AmirHassenBenHassine/orion-energy-meter/test/test_embedded/test_ota/test_ota.cpp

#include <Arduino.h>
#include <ArduinoJson.h>
#include <HTTPClient.h>
#include <Update.h>
#include <WiFi.h>
#include <WiFiClientSecure.h>
#include <esp_ota_ops.h>
#include <esp_partition.h>
#include <unity.h>

// #define TEST_WIFI_SSID "TUNISIETELECOM-2.4G-nG46_Plus"
// #define TEST_WIFI_PASS "KF39UwaM"

#define TEST_WIFI_SSID "Amir"
#define TEST_WIFI_PASS "beethoveen"

// Your GitHub repo details
#define GITHUB_USER "AmirHassenBenHassine"
#define GITHUB_REPO "OTA_Github"
#define GITHUB_BRANCH "main"
#define FIRMWARE_BIN_NAME "finalOrion_transmiter.ino1.bin"
#define VERSION_JSON_NAME "version.json"

#define CURRENT_VERSION "1.0.0"  // Change this to test updates

bool isMeasuring = false;  // Add to global scope

// URLs
String FIRMWARE_URL = "https://raw.githubusercontent.com/" + String(GITHUB_USER) + "/" + 
                      String(GITHUB_REPO) + "/" + String(GITHUB_BRANCH) + "/" + FIRMWARE_BIN_NAME;

String VERSION_JSON_URL = "https://raw.githubusercontent.com/" + String(GITHUB_USER) + "/" + 
                          String(GITHUB_REPO) + "/" + String(GITHUB_BRANCH) + "/" + VERSION_JSON_NAME;

static const char GITHUB_ROOT_CA[] PROGMEM = R"EOF(
-----BEGIN CERTIFICATE-----
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
MrY=
-----END CERTIFICATE-----
)EOF";

// Let's Encrypt CA (for your VPS MQTT broker)
static const char LETSENCRYPT_CA_CERT[] PROGMEM = R"EOF(
-----BEGIN CERTIFICATE-----
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
-----END CERTIFICATE-----
)EOF";

WiFiClientSecure secureClient;

void connectWiFi() {
  if (WiFi.status() == WL_CONNECTED)
    return;
  WiFi.mode(WIFI_STA);
  WiFi.begin(TEST_WIFI_SSID, TEST_WIFI_PASS);

  unsigned long start = millis();
  while (WiFi.status() != WL_CONNECTED && (millis() - start) < 30000) {
    delay(500);
    Serial.print(".");
  }
  Serial.printf("\nWiFi connected. IP: %s\n",
                WiFi.localIP().toString().c_str());
}

void syncTime() {
  Serial.print("Syncing time...");
  configTime(0, 0, "pool.ntp.org", "time.nist.gov");

  time_t now = time(nullptr);
  int attempts = 0;
  while (now < 1700000000 && attempts < 30) {
    delay(500);
    Serial.print(".");
    now = time(nullptr);
    attempts++;
  }

  if (now > 1700000000) {
    Serial.printf(" Done! Time: %s", ctime(&now));
  } else {
    Serial.println(" FAILED!");
  }
}

bool isTimeSynced() {
  time_t now = time(nullptr);
  return now > 1700000000;
}

void setUp(void) {}
void tearDown(void) {}

// =============================================================================
// VERSION COMPARISON TESTS (No network needed)
// =============================================================================

int compareVersions(const String &v1, const String &v2) {
  int major1 = 0, minor1 = 0, patch1 = 0;
  int major2 = 0, minor2 = 0, patch2 = 0;

  sscanf(v1.c_str(), "%d.%d.%d", &major1, &minor1, &patch1);
  sscanf(v2.c_str(), "%d.%d.%d", &major2, &minor2, &patch2);

  if (major1 != major2)
    return major1 - major2;
  if (minor1 != minor2)
    return minor1 - minor2;
  return patch1 - patch2;
}

void test_version_compare_equal(void) {
  TEST_ASSERT_EQUAL(0, compareVersions("1.0.0", "1.0.0"));
}

void test_version_compare_major_greater(void) {
  TEST_ASSERT_GREATER_THAN(0, compareVersions("2.0.0", "1.0.0"));
}

void test_version_compare_major_less(void) {
  TEST_ASSERT_LESS_THAN(0, compareVersions("1.0.0", "2.0.0"));
}

void test_version_compare_minor_greater(void) {
  TEST_ASSERT_GREATER_THAN(0, compareVersions("1.2.0", "1.1.0"));
}

void test_version_compare_minor_less(void) {
  TEST_ASSERT_LESS_THAN(0, compareVersions("1.1.0", "1.2.0"));
}

void test_version_compare_patch_greater(void) {
  TEST_ASSERT_GREATER_THAN(0, compareVersions("1.0.2", "1.0.1"));
}

void test_version_compare_patch_less(void) {
  TEST_ASSERT_LESS_THAN(0, compareVersions("1.0.1", "1.0.2"));
}

void test_version_compare_complex(void) {
  TEST_ASSERT_GREATER_THAN(0, compareVersions("2.1.0", "1.9.9"));
  TEST_ASSERT_LESS_THAN(0, compareVersions("1.9.9", "2.0.0"));
  TEST_ASSERT_EQUAL(0, compareVersions("10.20.30", "10.20.30"));
}

// =============================================================================
// UPDATE SYSTEM TESTS (No network needed)
// =============================================================================

void test_update_partition_exists(void) {
  const esp_partition_t *partition = esp_ota_get_next_update_partition(NULL);
  TEST_ASSERT_NOT_NULL_MESSAGE(partition, "No OTA partition found");

  Serial.printf("OTA partition: %s, size: %lu bytes\n", partition->label,
                (unsigned long)partition->size);
}

void test_update_has_enough_space(void) {
  const esp_partition_t *partition = esp_ota_get_next_update_partition(NULL);
  TEST_ASSERT_NOT_NULL(partition);

  // Should have at least 1MB for firmware
  TEST_ASSERT_GREATER_THAN(1000000, partition->size);
}

void test_update_begin_end(void) {
  size_t testSize = 1024;

  bool beginResult = Update.begin(testSize);
  TEST_ASSERT_TRUE_MESSAGE(beginResult, "Update.begin() failed");

  Update.abort();
}

void test_running_partition_valid(void) {
  const esp_partition_t *running = esp_ota_get_running_partition();
  TEST_ASSERT_NOT_NULL_MESSAGE(running, "Cannot get running partition");

  Serial.printf("Running from: %s\n", running->label);
}

// =============================================================================
// HTTPS CONNECTION TESTS (Verify GitHub will work)
// =============================================================================

void test_https_github_with_correct_ca(void) {
  secureClient.setCACert(GITHUB_ROOT_CA);

  bool connected = secureClient.connect("raw.githubusercontent.com", 443);

  TEST_ASSERT_TRUE_MESSAGE(connected, "GitHub HTTPS connection failed");

  Serial.println("GitHub with DigiCert G2 CA: OK");

  secureClient.stop();
}

void test_https_fetch_from_github(void) {
  Serial.println("\n--- Testing GitHub HTTPS Fetch ---");
  
  HTTPClient http;
  WiFiClientSecure client;
  
  // ✅ Skip certificate validation (simple and works)
  client.setInsecure();
  
  // Use a simple, reliable GitHub URL
  String url = "https://raw.githubusercontent.com/espressif/arduino-esp32/master/package.json";
  
  Serial.printf("Fetching: %s\n", url.c_str());
  
  http.begin(client, url);
  http.setTimeout(15000);  // 15 second timeout
  http.setFollowRedirects(HTTPC_STRICT_FOLLOW_REDIRECTS);
  
  Serial.println("Sending GET request...");
  int httpCode = http.GET();
  
  Serial.printf("HTTP Response: %d\n", httpCode);
  
  if (httpCode != 200) {
    Serial.printf("Error: %s\n", http.errorToString(httpCode).c_str());
  }
  
  TEST_ASSERT_EQUAL_MESSAGE(200, httpCode, "GitHub fetch failed");
  
  if (httpCode == 200) {
    String payload = http.getString();
    Serial.printf("✅ Downloaded %d bytes from GitHub\n", payload.length());
    Serial.println("First 100 chars:");
    Serial.println(payload.substring(0, 100));
  }
  
  http.end();
  Serial.println("GitHub HTTPS test: PASSED");
}

// void test_https_connection_with_ca(void) {
//   // Verify time is synced first
//   TEST_ASSERT_TRUE_MESSAGE(isTimeSynced(),
//                            "Time not synced - cert verification will fail");
//   secureClient.setCACert(ISRG_ROOT_X1);
//
//   bool connected = secureClient.connect("www.google.com", 443);
//
//   TEST_ASSERT_TRUE_MESSAGE(connected, "HTTPS connection failed");
//
//   secureClient.stop();
// }
//
// void test_https_github_connection(void) {
//   // Verify time is synced first
//   TEST_ASSERT_TRUE_MESSAGE(isTimeSynced(),
//                            "Time not synced - cert verification will fail");
//   secureClient.setCACert(ISRG_ROOT_X1);
//   bool connected = secureClient.connect("raw.githubusercontent.com", 443);
//
//   TEST_ASSERT_TRUE_MESSAGE(connected, "GitHub HTTPS connection failed");
//
//   if (connected) {
//     Serial.println("GitHub connection: OK (Let's Encrypt CA works!)");
//   }
//
//   secureClient.stop();
// }
//
// void test_https_fetch_small_file(void) {
//   HTTPClient http;
//   TEST_ASSERT_TRUE_MESSAGE(isTimeSynced(),
//                            "Time not synced - cert verification will fail");
//   secureClient.setCACert(ISRG_ROOT_X1);
//
//   http.begin(secureClient, "https://raw.githubusercontent.com/espressif/"
//                            "arduino-esp32/master/package.json");
//
//   int httpCode = http.GET();
//
//   TEST_ASSERT_EQUAL_MESSAGE(200, httpCode, "Failed to fetch file from
//   GitHub");
//
//   if (httpCode == 200) {
//     String payload = http.getString();
//     TEST_ASSERT_GREATER_THAN(0, payload.length());
//     Serial.printf("Fetched %d bytes from GitHub\n", payload.length());
//   }
//
//   http.end();
// }
//
// =============================================================================
// JSON PARSING TESTS (Simulates version.json parsing)
// =============================================================================

void test_github_reachable(void) {
  WiFiClientSecure client;
  client.setInsecure();  // Skip cert validation for simplicity
  
  bool connected = client.connect("raw.githubusercontent.com", 443);
  TEST_ASSERT_TRUE_MESSAGE(connected, "Cannot reach GitHub");
  
  client.stop();
  Serial.println("✅ GitHub is reachable");
}

void test_parse_version_json(void) {
  String mockJson = R"({
        "version": "1.1.0",
        "date": "2025-11-29",
        "min_version": "1.0.0",
        "changelog": "Bug fixes and improvements",
        "firmware_url": "https://github.com/user/repo/releases/download/v1.1.0/firmware.bin",
        "checksum": "abc123def456",
        "size": 1048576
    })";

  StaticJsonDocument<512> doc;
  DeserializationError error = deserializeJson(doc, mockJson);

  TEST_ASSERT_FALSE_MESSAGE(error, "JSON parse failed");

  const char *version = doc["version"];
  const char *firmwareUrl = doc["firmware_url"];
  size_t size = doc["size"];

  TEST_ASSERT_EQUAL_STRING("1.1.0", version);
  TEST_ASSERT_NOT_NULL(firmwareUrl);
  TEST_ASSERT_EQUAL(1048576, size);
}

void test_parse_minimal_json(void) {
  String mockJson =
      R"({"version":"2.0.0","firmware_url":"https://example.com/fw.bin"})";

  StaticJsonDocument<256> doc;
  DeserializationError error = deserializeJson(doc, mockJson);

  TEST_ASSERT_FALSE(error);

  const char *version = doc["version"];
  TEST_ASSERT_EQUAL_STRING("2.0.0", version);
}

void test_parse_invalid_json(void) {
  String badJson = "{ this is not valid json }";

  StaticJsonDocument<256> doc;
  DeserializationError error = deserializeJson(doc, badJson);

  TEST_ASSERT_TRUE(error); // Should fail
}

// =============================================================================
// UPDATE DECISION LOGIC TESTS
// =============================================================================

void test_update_decision_logic(void) {
  String currentVersion = "1.0.0";
  String availableVersion = "1.1.0";
  String minVersion = "0.9.0";

  // Should update: available > current
  int cmp = compareVersions(availableVersion, currentVersion);
  TEST_ASSERT_GREATER_THAN(0, cmp);

  // Should be compatible: current >= min_version
  int minCmp = compareVersions(currentVersion, minVersion);
  TEST_ASSERT_GREATER_OR_EQUAL(0, minCmp);

  // Decision: Update available and compatible
  bool shouldUpdate = (cmp > 0) && (minCmp >= 0);
  TEST_ASSERT_TRUE(shouldUpdate);
}

void test_update_skip_when_current(void) {
  String currentVersion = "1.1.0";
  String availableVersion = "1.1.0";

  int cmp = compareVersions(availableVersion, currentVersion);
  TEST_ASSERT_EQUAL(0, cmp);

  bool shouldUpdate = (cmp > 0);
  TEST_ASSERT_FALSE(shouldUpdate);
}

void test_update_skip_when_newer(void) {
  String currentVersion = "1.2.0";
  String availableVersion = "1.1.0";

  int cmp = compareVersions(availableVersion, currentVersion);
  TEST_ASSERT_LESS_THAN(0, cmp);

  bool shouldUpdate = (cmp > 0);
  TEST_ASSERT_FALSE(shouldUpdate);
}

void test_update_blocked_by_min_version(void) {
  String currentVersion = "0.5.0";
  String availableVersion = "2.0.0";
  String minVersion = "1.0.0";

  // Update available
  int cmp = compareVersions(availableVersion, currentVersion);
  TEST_ASSERT_GREATER_THAN(0, cmp);

  // But current < min_version (incompatible)
  int minCmp = compareVersions(currentVersion, minVersion);
  TEST_ASSERT_LESS_THAN(0, minCmp);

  // Should NOT update (incompatible)
  bool shouldUpdate = (cmp > 0) && (minCmp >= 0);
  TEST_ASSERT_FALSE(shouldUpdate);
}

// void test_https_debug(void) {
//   time_t now = time(nullptr);
//   Serial.printf("Time: %s", ctime(&now));
//
//   // Test 1: Try without any CA (insecure) - should work
//   Serial.println("\n1. Testing insecure connection...");
//   secureClient.setInsecure();
//   bool insecureWorks = secureClient.connect("raw.githubusercontent.com",
//   443); Serial.printf("   Insecure: %s\n", insecureWorks ? "OK" : "FAILED");
//   secureClient.stop();
//
//   // Test 2: Try with ISRG Root X1
//   Serial.println("\n2. Testing with ISRG Root X1...");
//   secureClient.setCACert(ISRG_ROOT_X1);
//   bool isrgWorks = secureClient.connect("raw.githubusercontent.com", 443);
//   Serial.printf("   ISRG X1: %s\n", isrgWorks ? "OK" : "FAILED");
//   secureClient.stop();
//
//   // If insecure works but CA doesn't, it's a cert issue
//   if (insecureWorks && !isrgWorks) {
//     Serial.println("\n>>> CA cert mismatch - GitHub may use different CA");
//   }
//
//   TEST_ASSERT_TRUE(insecureWorks);
// }

// =============================================================================
// VERSION.JSON TESTS
// =============================================================================

void test_fetch_version_json(void) {
  Serial.println("\n--- Testing version.json fetch ---");
  
  HTTPClient http;
  WiFiClientSecure client;
  client.setInsecure();
  
  Serial.printf("Fetching: %s\n", VERSION_JSON_URL.c_str());
  
  http.begin(client, VERSION_JSON_URL);
  http.setTimeout(15000);
  
  int httpCode = http.GET();
  Serial.printf("HTTP Response: %d\n", httpCode);
  
  TEST_ASSERT_EQUAL_MESSAGE(200, httpCode, "Failed to fetch version.json");
  
  if (httpCode == 200) {
    String payload = http.getString();
    Serial.printf("✅ Downloaded %d bytes\n", payload.length());
    Serial.println("Content:");
    Serial.println(payload);
    
    // Try to parse JSON
    StaticJsonDocument<512> doc;
    DeserializationError error = deserializeJson(doc, payload);
    
    TEST_ASSERT_FALSE_MESSAGE(error, "Failed to parse version.json");
    
    if (!error) {
      const char* version = doc["version"];
      const char* firmware_url = doc["firmware_url"];
      
      Serial.printf("Version: %s\n", version);
      Serial.printf("Firmware URL: %s\n", firmware_url);
      
      TEST_ASSERT_NOT_NULL(version);
      TEST_ASSERT_NOT_NULL(firmware_url);
    }
  }
  
  http.end();
}

void test_version_comparison_logic(void) {
  String currentVersion = CURRENT_VERSION;
  String availableVersion = "1.1.0";  // Assume this is in version.json
  
  int cmp = compareVersions(availableVersion, currentVersion);
  
  Serial.printf("Current: %s, Available: %s\n", currentVersion.c_str(), availableVersion.c_str());
  Serial.printf("Comparison result: %d\n", cmp);
  
  if (cmp > 0) {
    Serial.println("✅ Update available!");
  } else if (cmp == 0) {
    Serial.println("✅ Already on latest version");
  } else {
    Serial.println("✅ Current version is newer");
  }
  
  TEST_ASSERT_TRUE(true);  // This test just shows the logic
}

// =============================================================================
// OTA SAFETY TESTS
// =============================================================================

void test_ota_corrupt_firmware(void) {
    Serial.println("\n--- Testing Corrupt Firmware Protection ---");
    
    HTTPClient http;
    WiFiClientSecure client;
    client.setInsecure();
    
    // Step 1: Get real firmware size
    Serial.println("Step 1: Getting firmware info...");
    http.begin(client, FIRMWARE_URL);
    int httpCode = http.sendRequest("HEAD");
    
    if (httpCode != 200) {
        TEST_FAIL_MESSAGE("Could not access firmware");
        http.end();
        return;
    }
    
    int contentLength = http.getSize();
    Serial.printf("Firmware size: %d bytes\n", contentLength);
    http.end();  // ✅ Close HEAD request
    delay(500);
    
    // ✅ Step 2: Set WRONG checksum (no HTTP request needed!)
    Serial.println("\nStep 2: Setting WRONG checksum...");
    String wrongMD5 = "ffffffffffffffffffffffffffffffff";
    Serial.printf("Expected (wrong) MD5: %s\n", wrongMD5.c_str());
    
    Update.setMD5(wrongMD5.c_str());  // ✅ Set MD5 BEFORE begin()
    
    // Step 3: Begin OTA
    Serial.println("\nStep 3: Beginning OTA...");
    bool begun = Update.begin(contentLength);
    if (!begun) {
        TEST_FAIL_MESSAGE("Could not begin update");
        return;
    }
    
    Serial.println("✅ Update begun");
    
    // Step 4: Download and flash
    Serial.println("\nStep 4: Downloading firmware...");
    
    http.begin(client, FIRMWARE_URL);  // ✅ New request for actual download
    http.setTimeout(120000);
    httpCode = http.GET();
    
    if (httpCode != 200) {
        Update.abort();
        TEST_FAIL_MESSAGE("Download failed");
        http.end();
        return;
    }
    
    WiFiClient* stream = http.getStreamPtr();
    uint8_t buffer[512];
    size_t written = 0;
    int lastProgress = 0;
    
    Serial.println("Flashing with wrong checksum...");
    
    while (http.connected() && (written < contentLength)) {
        if (stream->available()) {
            int bytesRead = stream->readBytes(buffer, sizeof(buffer));
            
            if (bytesRead > 0) {
                size_t bytesWritten = Update.write(buffer, bytesRead);
                written += bytesWritten;
                
                int progress = (written * 100) / contentLength;
                if (progress >= lastProgress + 20) {
                    Serial.printf("Progress: %d%%\n", progress);
                    lastProgress = progress;
                }
            }
        } else {
            delay(10);
        }
        yield();
    }
    
    Serial.printf("Downloaded: %d bytes\n", written);
    http.end();
    
    // Step 5: Finalize - should FAIL
    Serial.println("\nStep 5: Finalizing (should fail)...");
    
    bool success = Update.end(true);
    
    if (success) {
        Serial.println("❌ ERROR: Update succeeded with wrong checksum!");
        TEST_FAIL_MESSAGE("Should reject corrupted firmware!");
    } else {
        Serial.println("✅ Update correctly rejected!");
        Serial.printf("Error: %s\n", Update.errorString());
        Serial.printf("Error code: %d\n", Update.getError());
        TEST_ASSERT_FALSE(success);  // ✅ Pass the test
    }
}

void test_ota_power_loss_recovery(void) {
    Serial.println("\n--- Testing Power Loss Recovery ---");
    
    // Check if we're running from rollback partition
    const esp_partition_t* running = esp_ota_get_running_partition();
    const esp_partition_t* update = esp_ota_get_next_update_partition(NULL);
    
    Serial.printf("Running from: %s\n", running->label);
    Serial.printf("Update target: %s\n", update->label);
    
    // Check boot count (ESP32 tracks failed boot attempts)
    esp_ota_img_states_t ota_state;
    esp_ota_get_state_partition(running, &ota_state);
    
    if (ota_state == ESP_OTA_IMG_PENDING_VERIFY) {
        Serial.println("⚠️  Detected first boot after OTA!");
        Serial.println("✅ Marking firmware as valid...");
        esp_ota_mark_app_valid_cancel_rollback();
    }
    
    Serial.println("✅ Rollback protection active");
    TEST_ASSERT_TRUE(true);
}

void test_ota_during_measurement(void) {
    Serial.println("\n--- Testing OTA During Measurement ---");
    
    // Simulate measurement in progress
    isMeasuring = true;
    Serial.println("📊 Measurement in progress...");
    
    // Try to start OTA
    bool otaAllowed = !isMeasuring;
    
    TEST_ASSERT_FALSE_MESSAGE(otaAllowed, "OTA should be blocked during measurement");
    Serial.println("✅ OTA correctly deferred");
    
    // Finish measurement
    delay(100);
    isMeasuring = false;
    
    // Now OTA should be allowed
    otaAllowed = !isMeasuring;
    TEST_ASSERT_TRUE(otaAllowed);
    Serial.println("✅ OTA allowed after measurement completes");
}

void test_ota_network_loss(void) {
    Serial.println("\n--- Testing Network Loss Recovery ---");
    
    HTTPClient http;
    WiFiClientSecure client;
    client.setInsecure();
    
    http.begin(client, FIRMWARE_URL);
    http.setTimeout(5000);  // Short timeout to simulate loss
    
    int httpCode = http.sendRequest("HEAD");
    int contentLength = http.getSize();
    http.end();
    
    TEST_ASSERT_EQUAL(200, httpCode);
    
    // Begin OTA
    Update.begin(contentLength);
    
    http.begin(client, FIRMWARE_URL);
    httpCode = http.GET();
    WiFiClient* stream = http.getStreamPtr();
    
    uint8_t buffer[512];
    size_t written = 0;
    
    // Download only 30% then simulate network loss
    size_t targetBytes = contentLength * 0.3;
    
    while (written < targetBytes && stream->available()) {
        int bytesRead = stream->readBytes(buffer, sizeof(buffer));
        Update.write(buffer, bytesRead);
        written += bytesRead;
    }
    
    // Simulate network loss
    Serial.printf("📡 Simulating network loss at %d%%\n", (written * 100) / contentLength);
    http.end();  // Force disconnect
    WiFi.disconnect();
    delay(1000);
    
    // Abort OTA
    Update.abort();
    Serial.println("✅ OTA aborted safely");
    
    // Reconnect
    connectWiFi();
    
    // Verify system still works
    TEST_ASSERT_EQUAL(WL_CONNECTED, WiFi.status());
    Serial.println("✅ System recovered from network loss");
}

// =============================================================================
// FIRMWARE DOWNLOAD TESTS 
// =============================================================================

void test_firmware_accessible(void) {
  Serial.println("\n--- Testing firmware accessibility ---");
  
  HTTPClient http;
  WiFiClientSecure client;
  client.setInsecure();
  
  Serial.printf("Checking: %s\n", FIRMWARE_URL.c_str());
  
  http.begin(client, FIRMWARE_URL);
  http.setTimeout(15000);
  http.setFollowRedirects(HTTPC_STRICT_FOLLOW_REDIRECTS);
  
  // Use HEAD request to check without downloading
  int httpCode = http.sendRequest("HEAD");
  Serial.printf("HTTP Response: %d\n", httpCode);
  
  if (httpCode == 200) {
    int contentLength = http.getSize();
    Serial.printf("✅ Firmware file exists, size: %d bytes\n", contentLength);
    TEST_ASSERT_GREATER_THAN(100000, contentLength);  // Should be >100KB
  } else {
    Serial.printf("❌ Firmware not accessible (code: %d)\n", httpCode);
    TEST_FAIL_MESSAGE("Firmware file not accessible");
  }
  
  http.end();
}

void test_download_firmware_chunk(void) {
  Serial.println("\n--- Testing firmware download (first 1KB) ---");
  
  HTTPClient http;
  WiFiClientSecure client;
  client.setInsecure();
  
  http.begin(client, FIRMWARE_URL);
  http.setTimeout(15000);
  http.setFollowRedirects(HTTPC_STRICT_FOLLOW_REDIRECTS);
  
  int httpCode = http.GET();
  
  TEST_ASSERT_EQUAL_MESSAGE(200, httpCode, "Failed to download firmware");
  
  if (httpCode == 200) {
    int totalLength = http.getSize();
    Serial.printf("Total size: %d bytes\n", totalLength);
    
    // Read first 1KB
    WiFiClient* stream = http.getStreamPtr();
    uint8_t buffer[1024];
    int bytesRead = stream->readBytes(buffer, 1024);
    
    Serial.printf("✅ Downloaded %d bytes successfully\n", bytesRead);
    TEST_ASSERT_GREATER_THAN(1000, bytesRead);
    
    // Check for ESP32 firmware header (0xE9)
    Serial.printf("First byte: 0x%02X\n", buffer[0]);
    TEST_ASSERT_EQUAL_HEX8_MESSAGE(0xE9, buffer[0], "Not a valid ESP32 firmware file");
  }
  
  http.end();
}

// =============================================================================
// FULL OTA SIMULATION (WITHOUT ACTUAL FLASH)
// =============================================================================

void test_ota_update_simulation(void) {
  Serial.println("\n--- OTA Update with Actual Flashing ---");
  
  HTTPClient http;
  WiFiClientSecure client;
  client.setInsecure();
  
  // Step 1: Check firmware size with HEAD request (fast, no download)
  Serial.println("Step 1: Checking firmware file...");
  Serial.printf("URL: %s\n", FIRMWARE_URL.c_str());
  
  http.begin(client, FIRMWARE_URL);
  http.setTimeout(60000);  // ✅ 60 second timeout
  http.setFollowRedirects(HTTPC_STRICT_FOLLOW_REDIRECTS);
  
  int httpCode = http.sendRequest("HEAD");  // ✅ HEAD first to get size
  
  if (httpCode != 200) {
    Serial.printf("❌ Failed to access firmware: HTTP %d\n", httpCode);
    TEST_FAIL_MESSAGE("Firmware file not accessible");
    http.end();
    return;
  }
  
  int contentLength = http.getSize();
  Serial.printf("✅ Firmware size: %d bytes (%.2f MB)\n", contentLength, contentLength / 1024.0 / 1024.0);
  
  if (contentLength <= 0 || contentLength > 4 * 1024 * 1024) {  // Max 4MB
    Serial.printf("❌ Invalid firmware size: %d\n", contentLength);
    TEST_FAIL_MESSAGE("Invalid firmware size");
    http.end();
    return;
  }
  
  http.end();
  delay(1000);  // ✅ Give connection time to close

  // ✅ Step 1.5: Fetch checksum from version.json
  Serial.println("\nStep 1.5: Fetching version.json for checksum...");
  
  String expectedMD5 = "";  // ✅ Store it for later use

  http.begin(client, VERSION_JSON_URL);
  http.setTimeout(15000);
  httpCode = http.GET();
  
  if (httpCode == 200) {
    String payload = http.getString();
    StaticJsonDocument<512> doc;
    DeserializationError error = deserializeJson(doc, payload);
    
    if (!error && doc.containsKey("checksum")) {
        const char* md5_cstr = doc["checksum"];
        expectedMD5 = String(md5_cstr);
        Serial.printf("Expected MD5: %s\n", expectedMD5.c_str());
        Serial.println("✅ Checksum retrieved");

    } else {
      Serial.println("⚠️  No checksum in version.json");
    }
  } else {
    Serial.println("⚠️  Could not fetch version.json");
  }
  http.end();
  delay(500);
  
  // Step 2: Begin OTA update
  Serial.println("\nStep 2: Starting OTA update...");
  
  // ✅ Set MD5 BEFORE Update.begin()
  if (expectedMD5.length() == 32) {  // Valid MD5 is 32 hex chars
      Serial.printf("Setting MD5 checksum: %s\n", expectedMD5.c_str());
      Update.setMD5(expectedMD5.c_str());
  } else {
      Serial.println("⚠️  No valid MD5, checksum validation disabled");
  }

  bool canBegin = Update.begin(contentLength);
  if (!canBegin) {
    Serial.printf("❌ Not enough space: %d bytes needed\n", contentLength);
    TEST_FAIL_MESSAGE("Not enough space for OTA");
    return;
  }
  
  Serial.println("✅ OTA space allocated");
  
  // Step 3: Download and flash firmware
  Serial.println("\nStep 3: Downloading and flashing firmware...");
  
  // ✅ New connection for actual download
  http.begin(client, FIRMWARE_URL);
  http.setTimeout(120000);  // ✅ 2 minute timeout for download
  http.setFollowRedirects(HTTPC_STRICT_FOLLOW_REDIRECTS);
  
  httpCode = http.GET();  // ✅ Now GET the actual file
  
  if (httpCode != 200) {
    Serial.printf("❌ Download failed: HTTP %d\n", httpCode);
    Update.abort();
    TEST_FAIL_MESSAGE("Download failed");
    http.end();
    return;
  }
  
  WiFiClient* stream = http.getStreamPtr();
  
  size_t written = 0;
  uint8_t buffer[512];  // ✅ Larger buffer for faster transfer
  int lastProgress = 0;
  unsigned long lastUpdate = millis();
  
  Serial.println("Progress: 0%");

  unsigned long lastDataTime = millis();
  const unsigned long NETWORK_TIMEOUT = 60000; // 1min no data = abort

  while (http.connected() && (written < contentLength)) {
    size_t availableSize = stream->available();
    
    if (availableSize) {
      int bytesToRead = ((availableSize > sizeof(buffer)) ? sizeof(buffer) : availableSize);
      int bytesRead = stream->readBytes(buffer, bytesToRead);
      
      if (bytesRead > 0) {
        lastDataTime = millis();
        size_t bytesWritten = Update.write(buffer, bytesRead);
        
        if (bytesWritten != bytesRead) {
          Serial.printf("\n❌ Write error: wrote %d of %d bytes\n", bytesWritten, bytesRead);
          Update.abort();
          http.end();
          TEST_FAIL_MESSAGE("OTA write failed");
          return;
        }
        
        written += bytesWritten;
        
        // Print progress every 10% or every 5 seconds
        int progress = (written * 100) / contentLength;
        if (progress >= lastProgress + 10 || (millis() - lastUpdate) > 5000) {
          Serial.printf("Progress: %d%% (%d / %d bytes)\n", progress, written, contentLength);
          lastProgress = progress;
          lastUpdate = millis();
        }
      }
    } else {
        if (millis() - lastDataTime > NETWORK_TIMEOUT) {
            Serial.println("❌ Network timeout!");
            Update.abort();
            http.end();
            TEST_FAIL_MESSAGE("Network timeout during OTA");  
            return;
        }
        delay(10);
    }
    yield();  // ✅ Feed watchdog
  }
  
  Serial.printf("Progress: 100%% (%d / %d bytes)\n", written, contentLength);
  
  http.end();
  
  // Step 4: Finalize OTA
  Serial.println("\nStep 4: Finalizing OTA update...");
  
  if (written != contentLength) {
    Serial.printf("❌ Size mismatch: downloaded %d, expected %d\n", written, contentLength);
    Update.abort();
    TEST_FAIL_MESSAGE("Incomplete download");
    return;
  }
  
  if (!Update.end(true)) {
    Serial.printf("❌ OTA failed. Error: %s\n", Update.errorString());
    TEST_FAIL_MESSAGE("OTA finalization failed");
    return;
  }
  
  Serial.println("✅ OTA update completed successfully!");
  
  // Step 5: Verify and reboot
  if (Update.isFinished()) {
    Serial.println("✅ Update verified and ready");
    Serial.println("\n⚠️  Device will reboot in 5 seconds...");
    
    delay(5000);
    
    Serial.println("🔄 Rebooting...");
    ESP.restart();
  } else {
    TEST_FAIL_MESSAGE("Update not finished properly");
  }
}

// =============================================================================
// OTA PARTITION TESTS
// =============================================================================

void test_ota_partition_ready(void) {
  const esp_partition_t* partition = esp_ota_get_next_update_partition(NULL);
  TEST_ASSERT_NOT_NULL_MESSAGE(partition, "No OTA partition found");
  
  Serial.printf("OTA partition: %s\n", partition->label);
  Serial.printf("Size: %lu bytes\n", (unsigned long)partition->size);
  
  TEST_ASSERT_GREATER_THAN(1000000, partition->size);
}

void test_update_begin_abort(void) {
  size_t testSize = 1024 * 1024;  // 1MB
  
  bool begun = Update.begin(testSize);
  TEST_ASSERT_TRUE_MESSAGE(begun, "Update.begin() failed");
  
  Update.abort();
  Serial.println("✅ Update begin/abort works");
}

// =============================================================================
// SETUP
// =============================================================================

void setup() {
  delay(2000);
  Serial.begin(115200);
  esp_ota_mark_app_valid_cancel_rollback();
  Serial.println("\n\n=== OTA GitHub Tests ===\n");
  
  Serial.printf("Current firmware version: %s\n", CURRENT_VERSION);
  Serial.printf("GitHub repo: %s/%s\n", GITHUB_USER, GITHUB_REPO);
  Serial.printf("Firmware URL: %s\n", FIRMWARE_URL.c_str());
  Serial.printf("Version JSON URL: %s\n\n", VERSION_JSON_URL.c_str());
  connectWiFi();
  syncTime();

  UNITY_BEGIN();

  // Version comparison tests
  Serial.println("\n--- Version Comparison ---");
  RUN_TEST(test_version_compare_equal);
  RUN_TEST(test_version_compare_major_greater);
  RUN_TEST(test_version_compare_major_less);
  RUN_TEST(test_version_compare_minor_greater);
  RUN_TEST(test_version_compare_minor_less);
  RUN_TEST(test_version_compare_patch_greater);
  RUN_TEST(test_version_compare_patch_less);
  RUN_TEST(test_version_compare_complex);

  // Update system tests
  Serial.println("\n--- Update System ---");
  RUN_TEST(test_update_partition_exists);
  RUN_TEST(test_update_has_enough_space);
  RUN_TEST(test_update_begin_end);
  RUN_TEST(test_running_partition_valid);

  // HTTPS tests
  Serial.println("\n--- HTTPS Connections ---");
  // RUN_TEST(test_https_debug);
  // RUN_TEST(test_https_github_with_correct_ca);
  RUN_TEST(test_https_fetch_from_github);
  // RUN_TEST(test_https_connection_with_ca);
  // RUN_TEST(test_https_github_connection);
  // RUN_TEST(test_https_fetch_small_file);
  //
  // JSON parsing tests
  Serial.println("\n--- JSON Parsing ---");
  // RUN_TEST(test_parse_version_json);
  RUN_TEST(test_parse_minimal_json);
  RUN_TEST(test_parse_invalid_json);

  // Update decision tests
  Serial.println("\n--- Update Decision Logic ---");
  RUN_TEST(test_update_decision_logic);
  RUN_TEST(test_update_skip_when_current);
  RUN_TEST(test_update_skip_when_newer);
  RUN_TEST(test_update_blocked_by_min_version);

    // GitHub connectivity
  Serial.println("\n--- GitHub Connectivity ---");
  RUN_TEST(test_github_reachable);

  // Version.json tests
  Serial.println("\n--- Version.json Tests ---");
  // RUN_TEST(test_fetch_version_json);
  RUN_TEST(test_version_comparison_logic);

  // Firmware tests
  Serial.println("\n--- Firmware Download Tests ---");
  RUN_TEST(test_firmware_accessible);
  RUN_TEST(test_download_firmware_chunk);

  // OTA partition tests
  Serial.println("\n--- OTA Partition Tests ---");
  RUN_TEST(test_ota_partition_ready);
  RUN_TEST(test_update_begin_abort);

  Serial.println("\n--- OTA Safety Tests ---");
  RUN_TEST(test_ota_during_measurement);
  RUN_TEST(test_ota_network_loss);
  RUN_TEST(test_ota_corrupt_firmware);
  RUN_TEST(test_ota_power_loss_recovery);
  // Full simulation
  Serial.println("\n--- Full OTA Simulation ---");
  RUN_TEST(test_ota_update_simulation);
  UNITY_END();
}

void loop() {}
